martin-wagner/saba-6-3d-fernbedienung-hw/doku/latex/ant1.jpeg

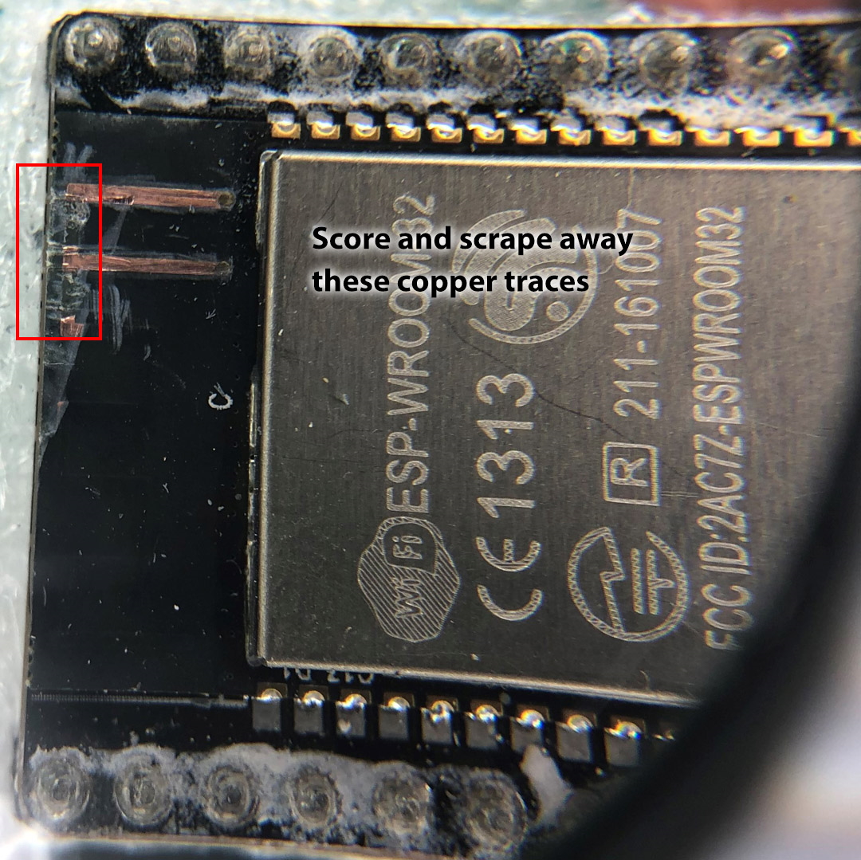
doku/latex/ant1.jpeg
