martin-wagner/saba-6-3d-fernbedienung-hw/doku/latex/ant2.jpeg

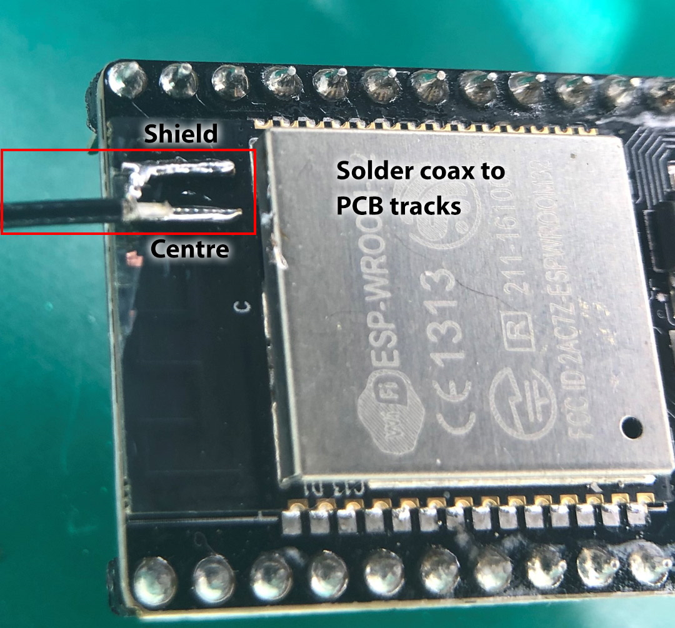
doku/latex/ant2.jpeg
