martin-wagner/saba-6-3d-fernbedienung-hw/doku/rechnungen-beispiele/2021-01-09 15.57.24 www.random-science-tools.com 3d192dff3986 suchlauf-langsam-schnell.jpg

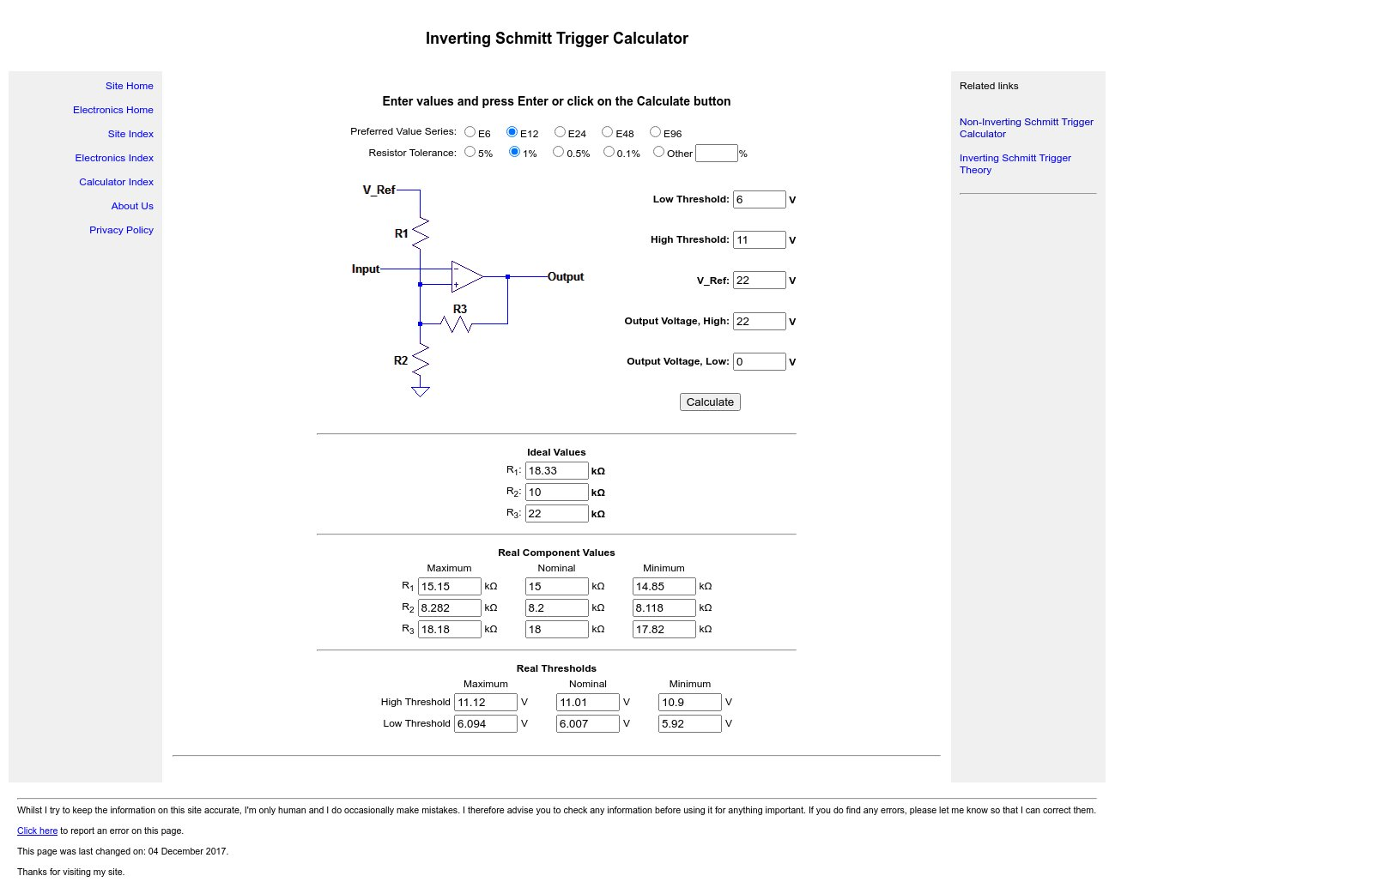
doku/rechnungen-beispiele/2021-01-09 15.57.24 www.random-science-tools.com 3d192dff3986 suchlauf-langsam-schnell.jpg
