martin-wagner/saba-6-3d-fernbedienung-hw/doku/rechnungen-beispiele/2021-04-10 11.28.31 www.random-science-tools.com 0c6ef2667732 phase-rev1b.jpg

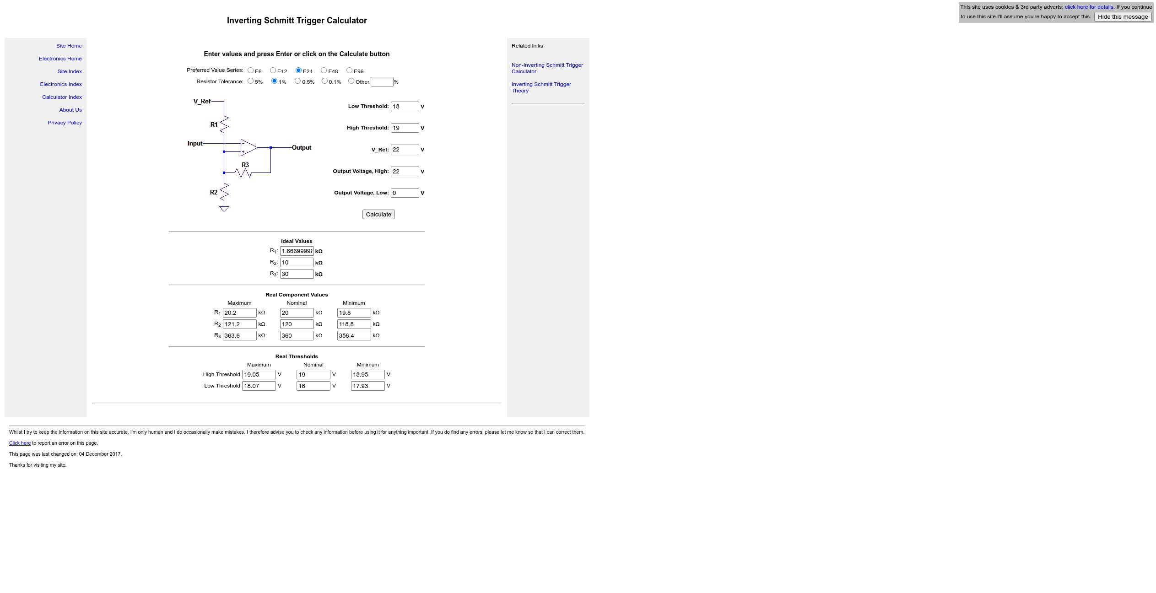
doku/rechnungen-beispiele/2021-04-10 11.28.31 www.random-science-tools.com 0c6ef2667732 phase-rev1b.jpg
