martin-wagner/saba-6-3d-fernbedienung-hw/doku/rechnungen-beispiele/2021-08-18 10.42.19 www.random-science-tools.com df0a42397f79 suchlauf-aus-langsam.jpg

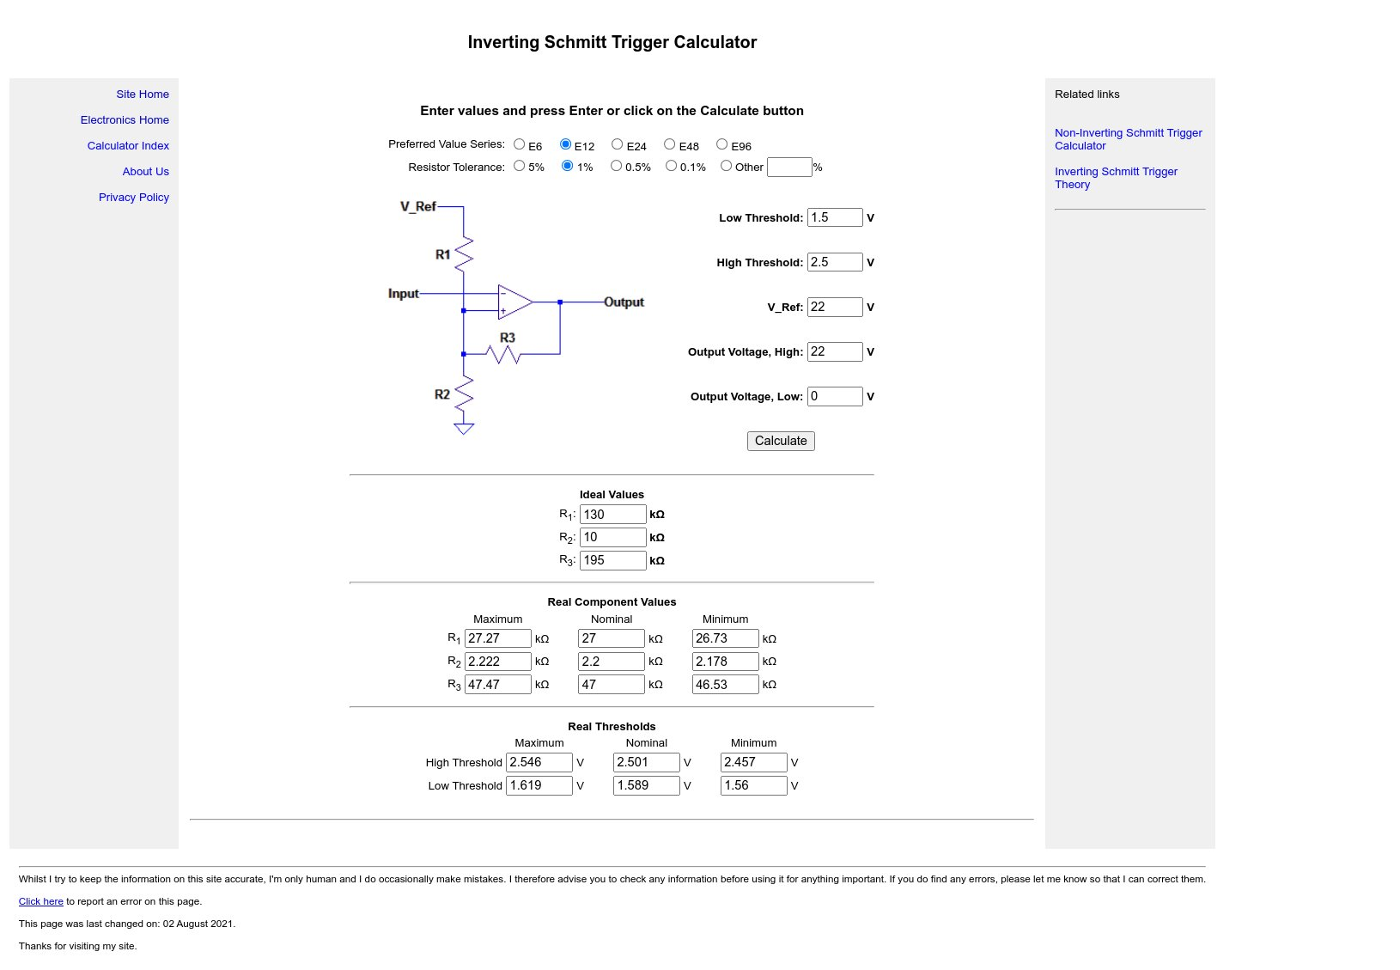
doku/rechnungen-beispiele/2021-08-18 10.42.19 www.random-science-tools.com df0a42397f79 suchlauf-aus-langsam.jpg
