martin-wagner/saba-6-3d-fernbedienung-hw/doku/rechnungen-beispiele/FB_Kontroller_Serie_5V.jpg

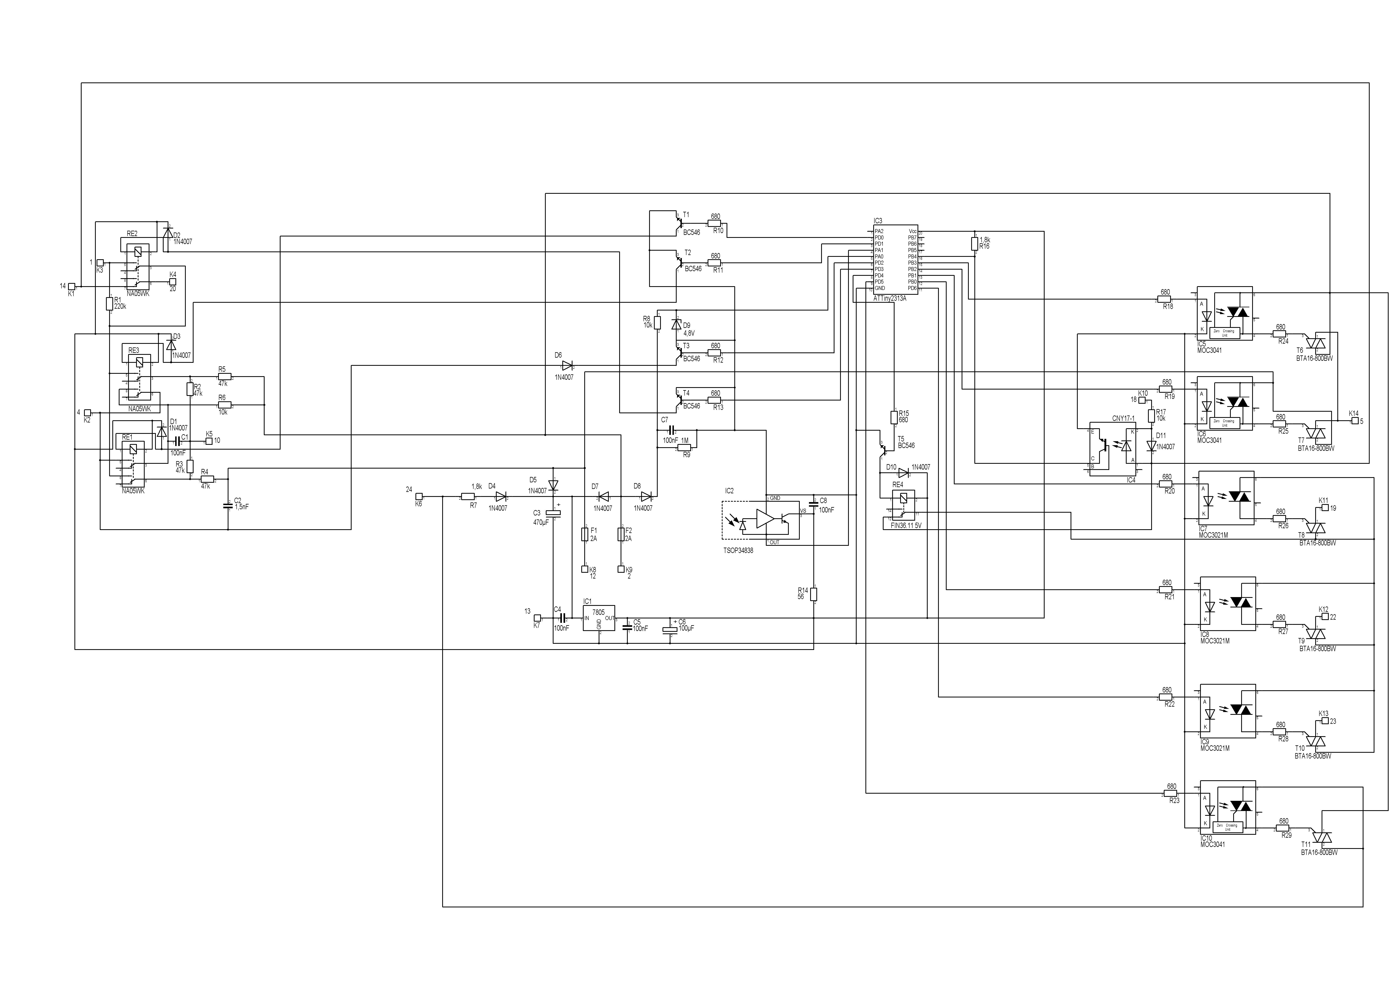
doku/rechnungen-beispiele/FB_Kontroller_Serie_5V.jpg
