martin-wagner/saba-6-3d-fernbedienung-hw/doku/rechnungen-beispiele/Saba_IR-Remote_Schema1.JPG

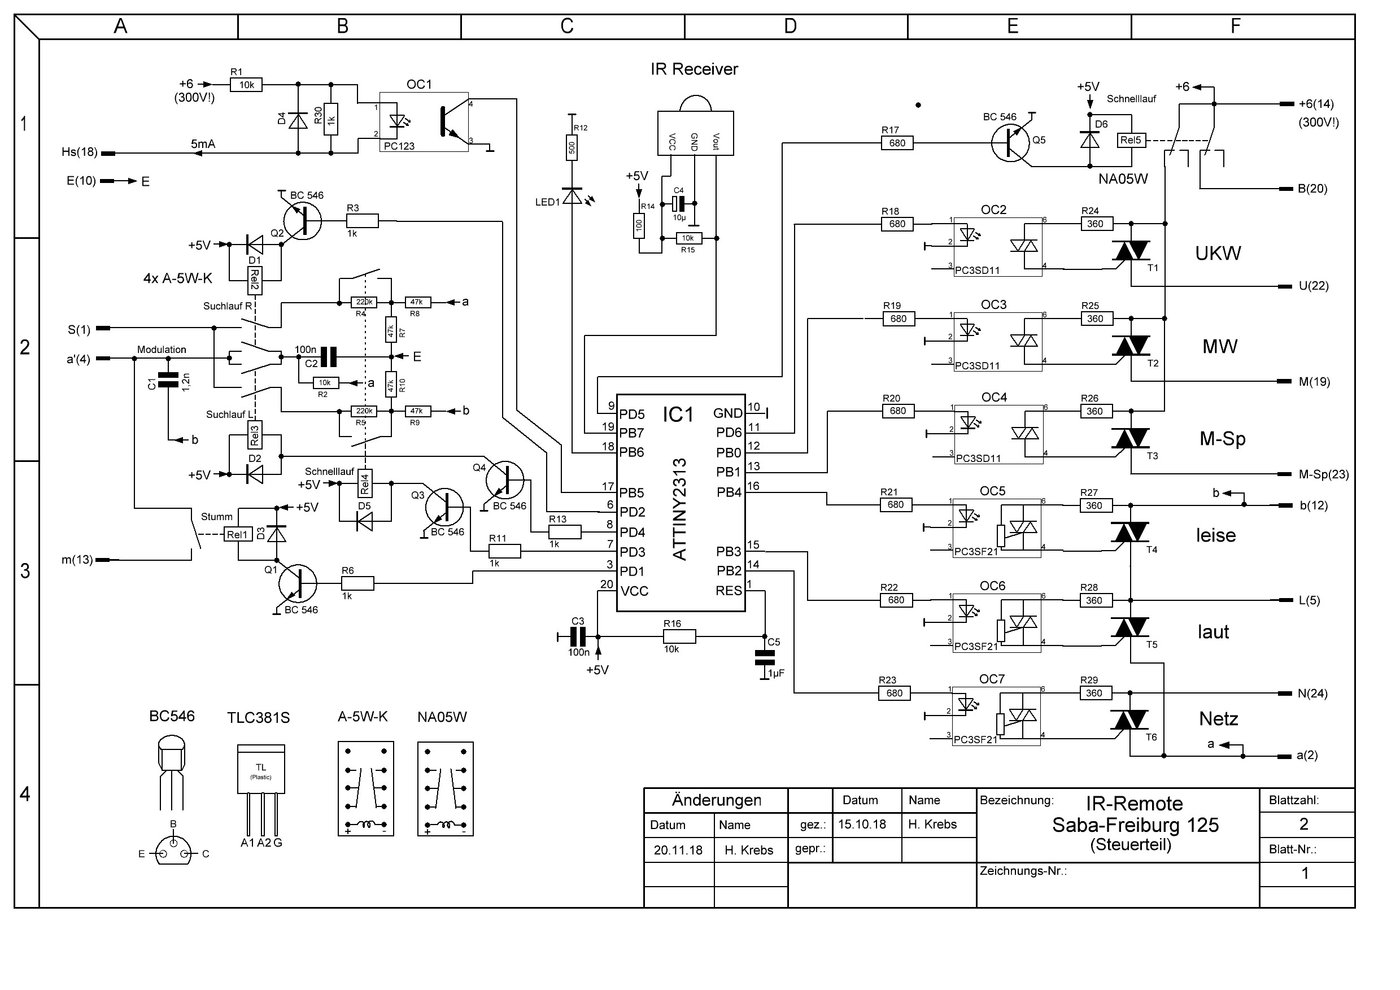
doku/rechnungen-beispiele/Saba_IR-Remote_Schema1.JPG
