martin-wagner/saba-6-3d-fernbedienung-hw/cad/pcb/saba-fernbedienung/rev1-a/scm/saba-fernbedienung.pdf

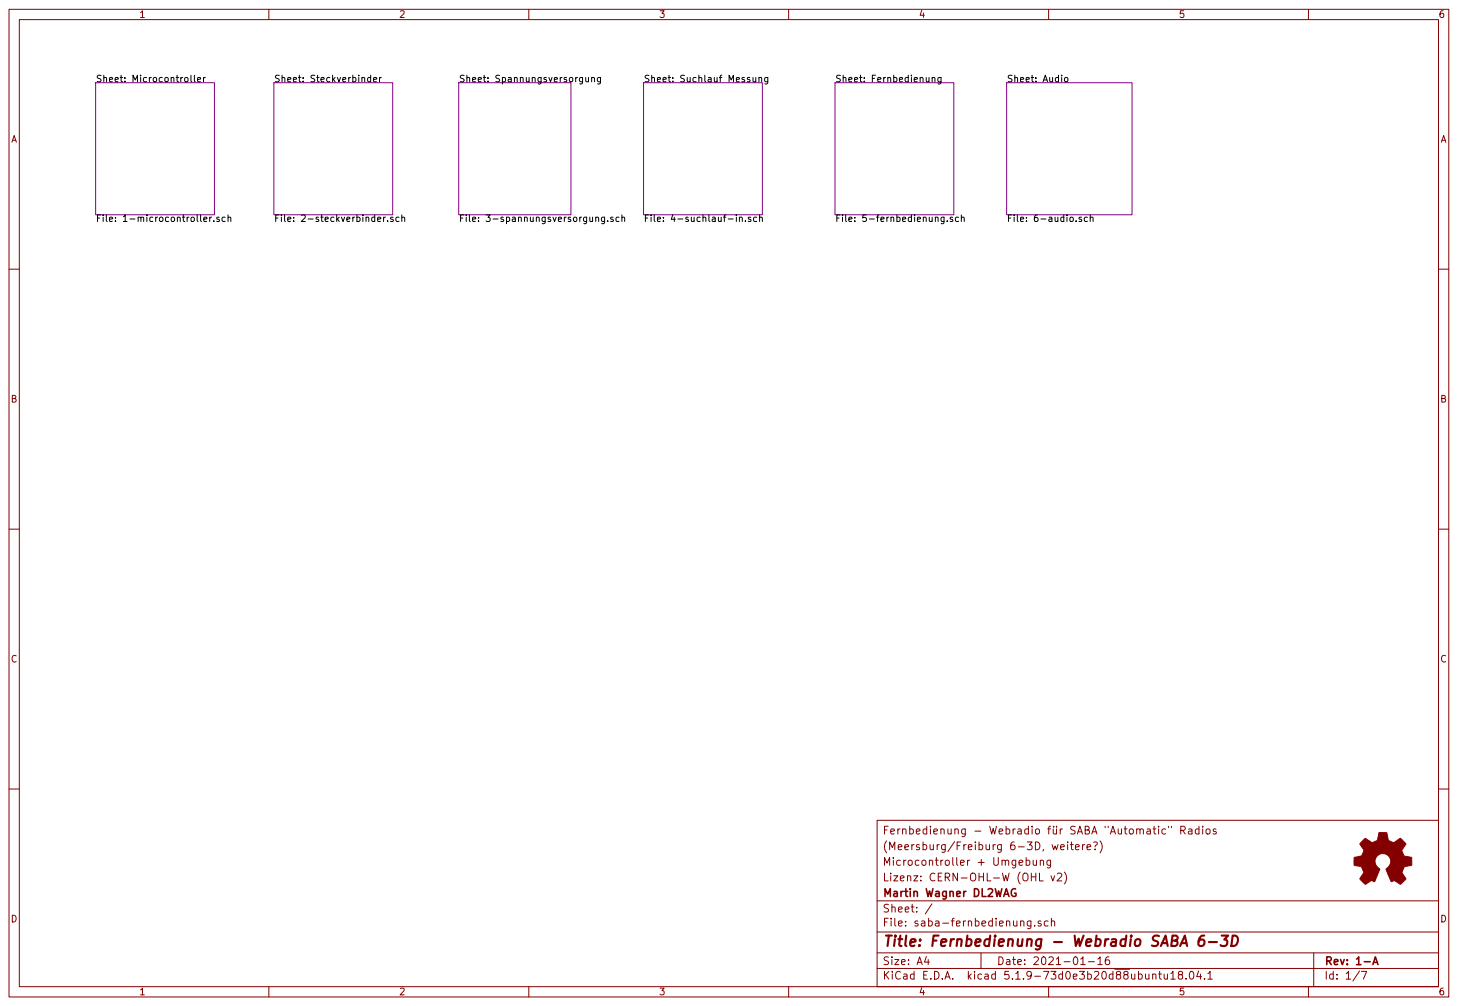
[picture p95: page 1]

Fernbedienung - Webradio für SABA "Automatic" Radios
(Meersburg/Freiburg 6-3D, weitere?)
Microcontroller + Umgebung
Lizenz: CERN-OHL-W (OHL v2)
File: saba-fernbedienung.sch Sheet: / Martin Wagner DL2WAG

Id: 1/7 Title: Fernbedienung - Webradio SABA 6-3D

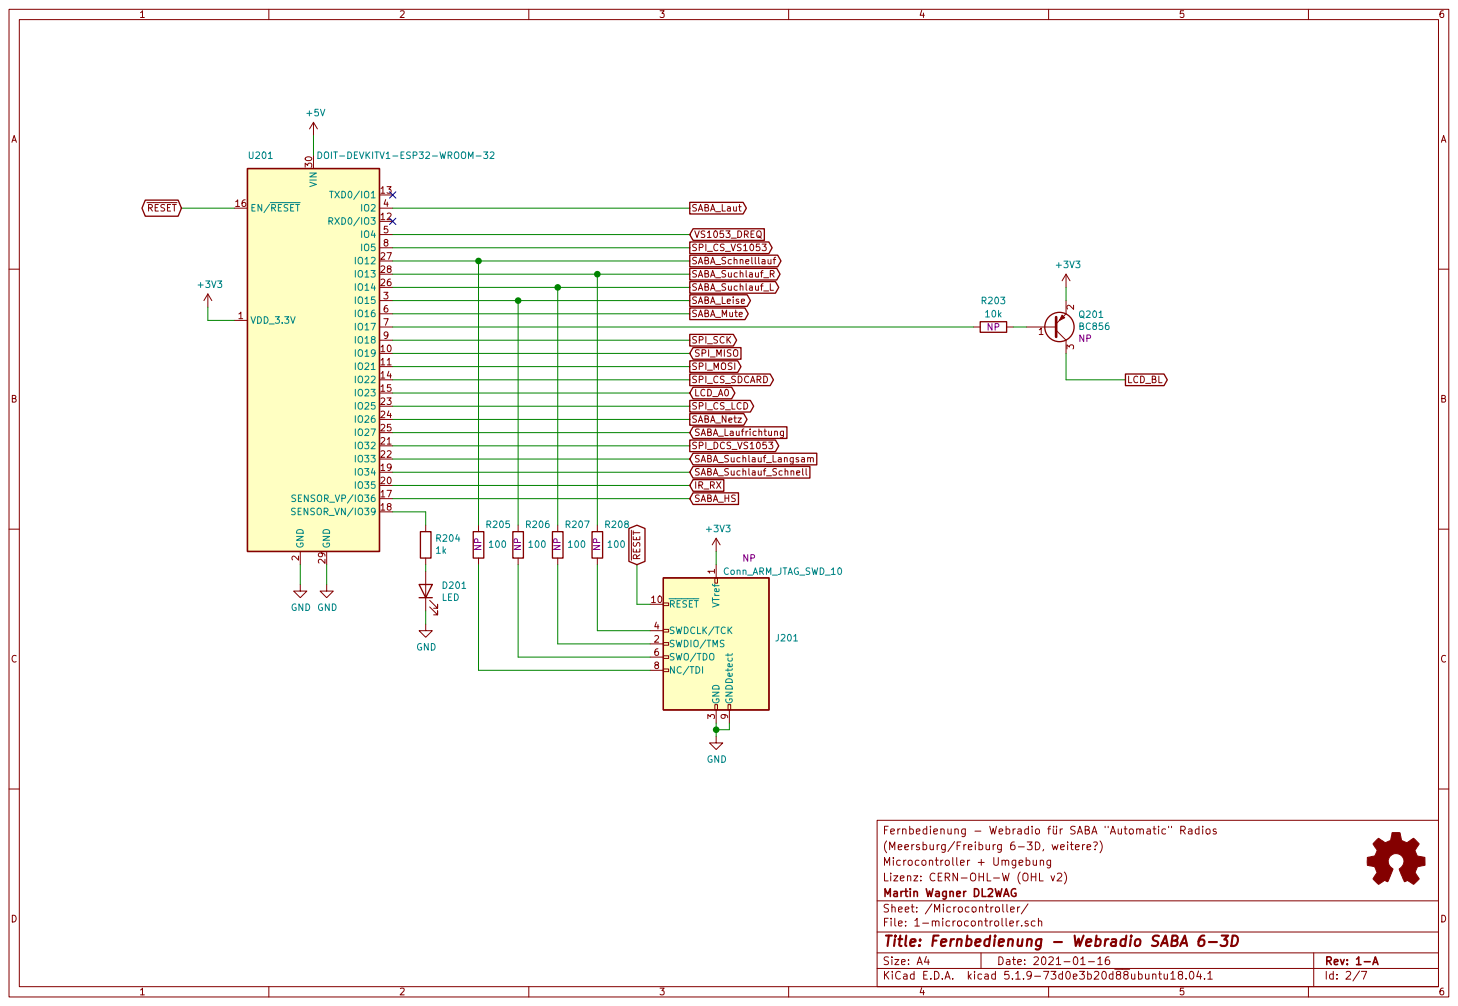
[picture p96: page 2]

3 SWDCLK/TCK 4 SWO/TDO 6 NC/TDI 8 GNDDetect 9

(Meersburg/Freiburg 6-3D, weitere?)
Microcontroller + Umgebung
Lizenz: CERN-OHL-W (OHL v2)
File: 1-microcontroller.sch Sheet: /Microcontroller/ Martin Wagner DL2WAG

Id: 2/7 Title: Fernbedienung - Webradio SABA 6-3D

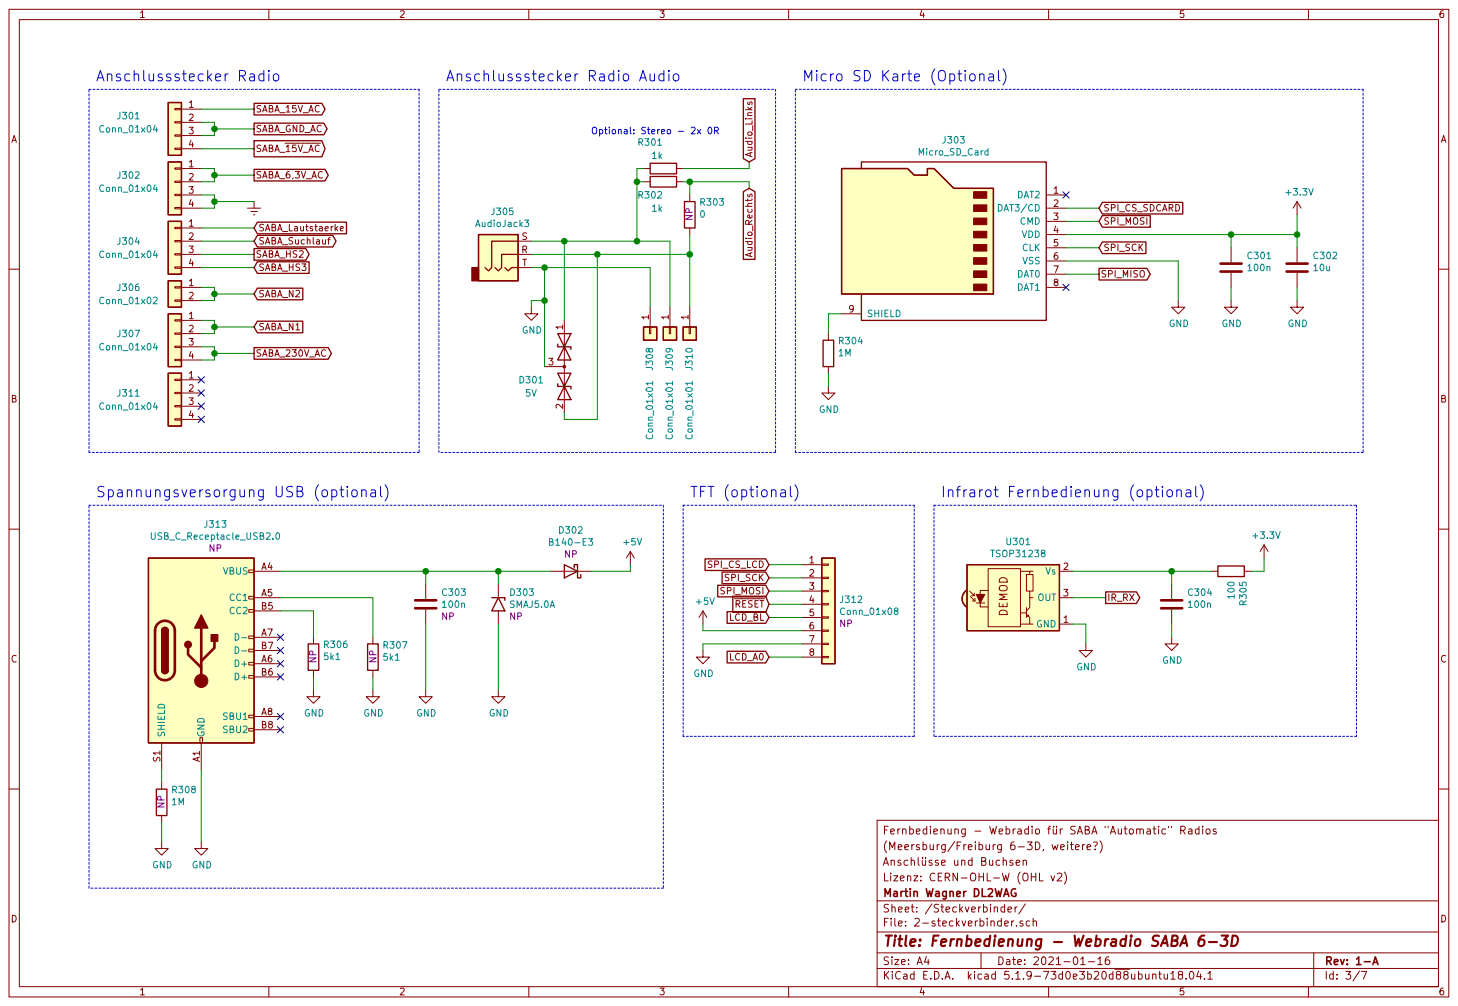
[picture p97: page 3]

Fernbedienung - Webradio für SABA "Automatic" Radios
(Meersburg/Freiburg 6-3D, weitere?)
Lizenz: CERN-OHL-W (OHL v2) Anschlüsse und Buchsen

File: 2-steckverbinder.sch Sheet: /Steckverbinder/ Martin Wagner DL2WAG

Id: 3/7 Title: Fernbedienung - Webradio SABA 6-3D

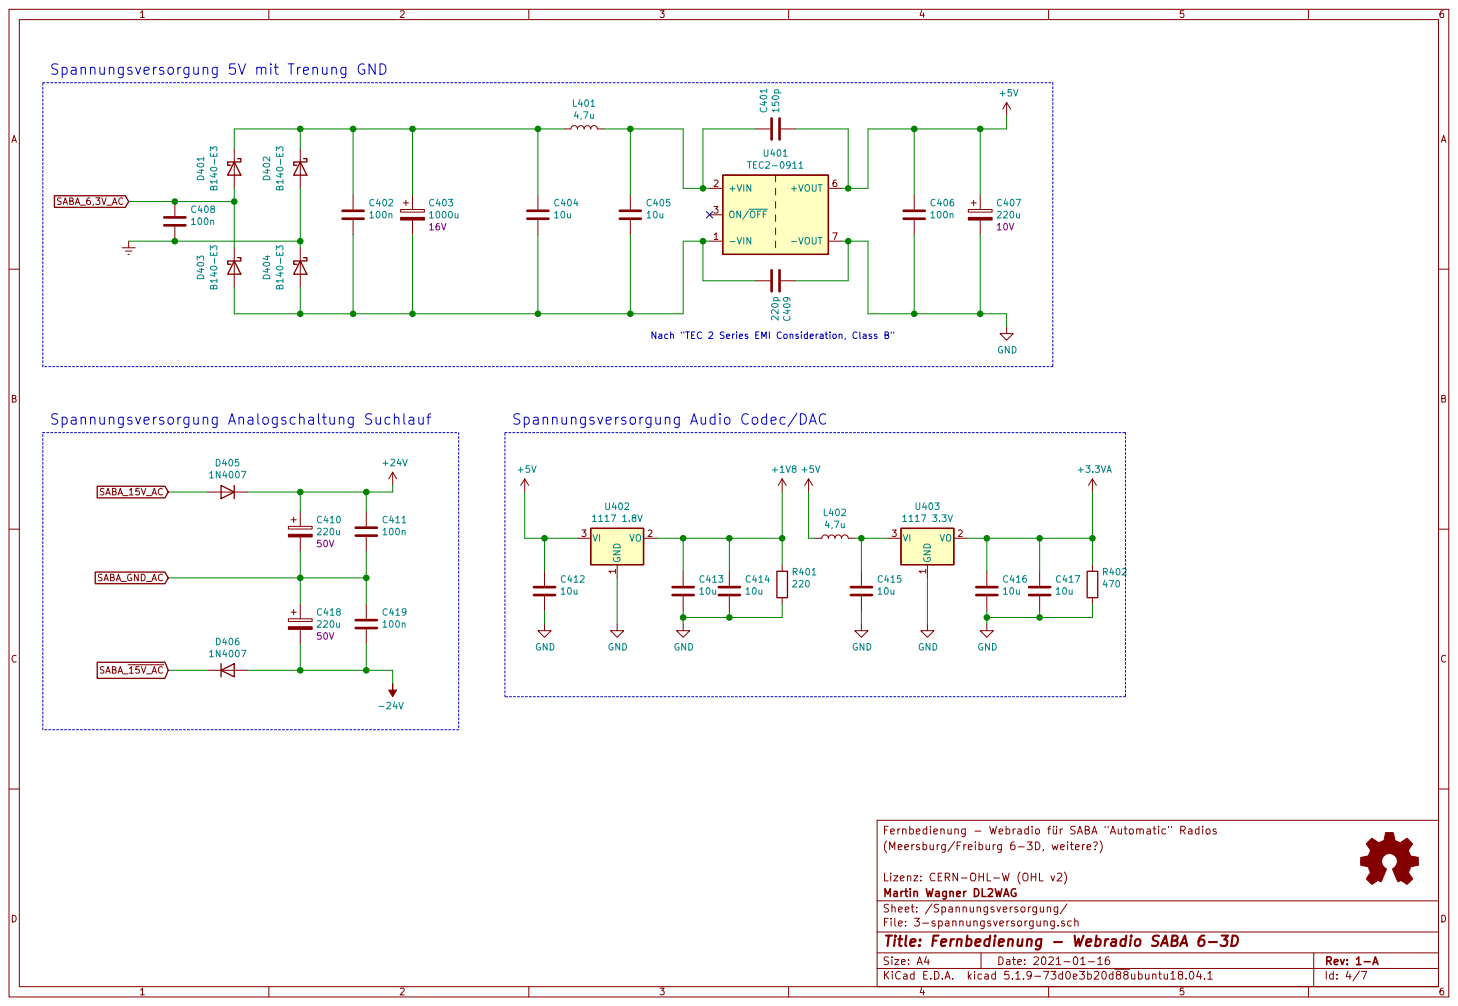
[picture p98: page 4]

Spannungsversorgung 5V mit Trenung GND

Nach "TEC 2 Series EMI Consideration, Class B" Spannungsversorgung Audio Codec/DAC

Fernbedienung - Webradio für SABA "Automatic" Radios
(Meersburg/Freiburg 6-3D, weitere?)

Lizenz: CERN-OHL-W (OHL v2)
Martin Wagner DL2WAG
Sheet: /Spannungsversorgung/
File: 3-spannungsversorgung.sch
Id: 4/7 Title: Fernbedienung - Webradio SABA 6-3D

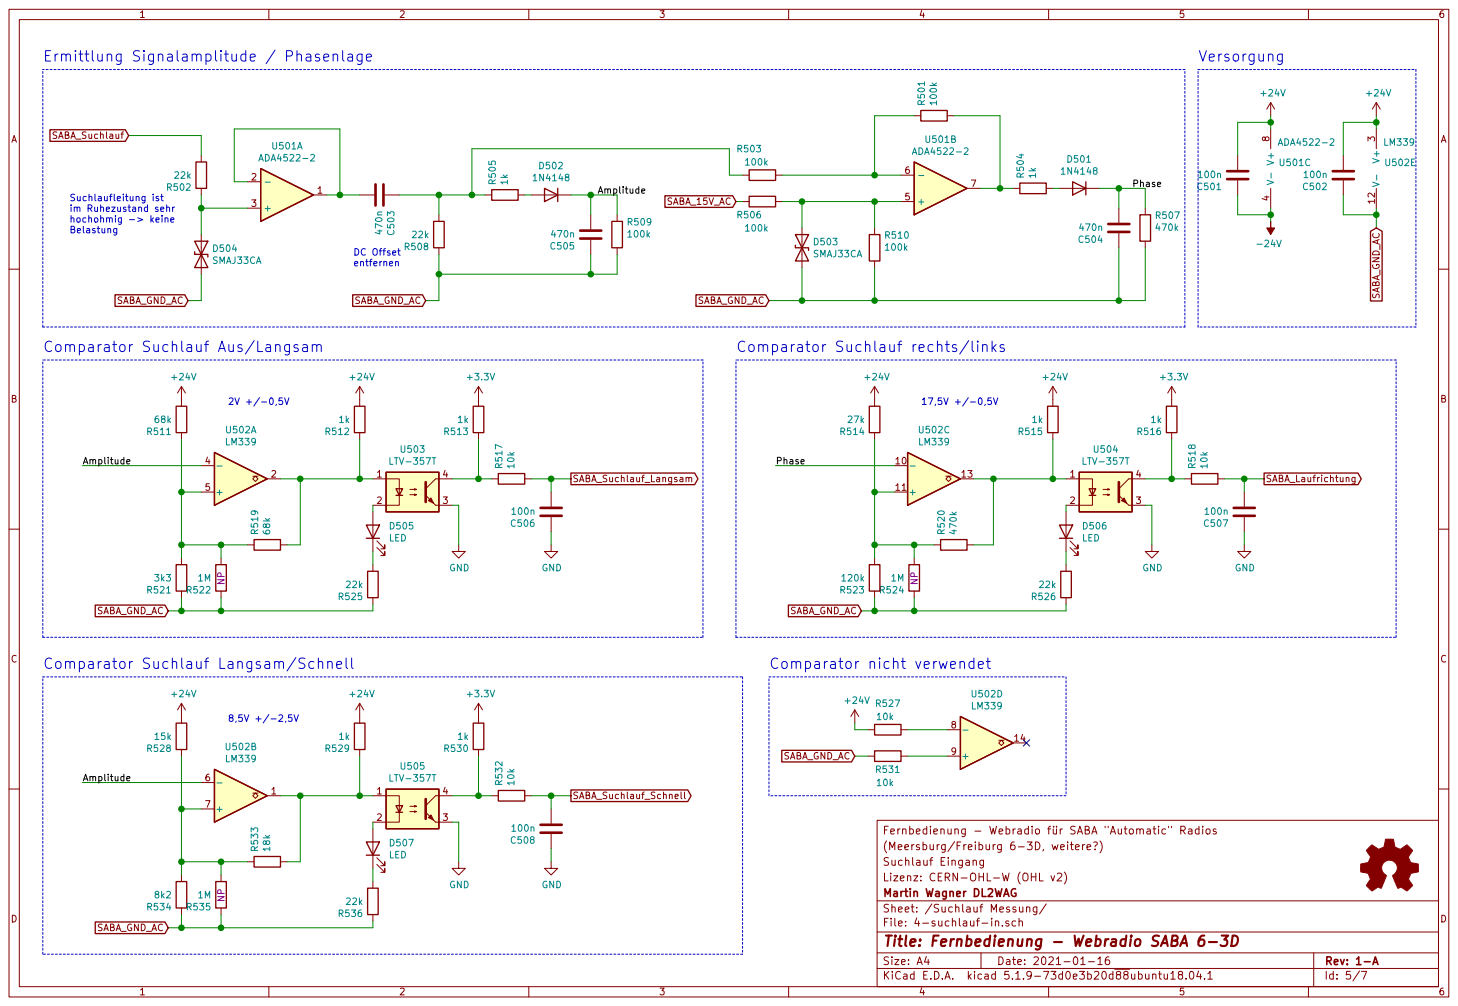
[picture p99: page 5]

Suchlaufleitung ist
im Ruhezustand sehr hochohmig -> keine

Comparator Suchlauf Aus/Langsam

Comparator Suchlauf rechts/links

2V +/-0,5V Comparator Suchlauf Langsam/Schnell

Fernbedienung - Webradio für SABA "Automatic" Radios R534

(Meersburg/Freiburg 6-3D, weitere?)
Suchlauf Eingang
Lizenz: CERN-OHL-W (OHL v2)
Martin Wagner DL2WAG
File: 4-suchlauf-in.sch Sheet: /Suchlauf Messung/
Id: 5/7 Title: Fernbedienung - Webradio SABA 6-3D

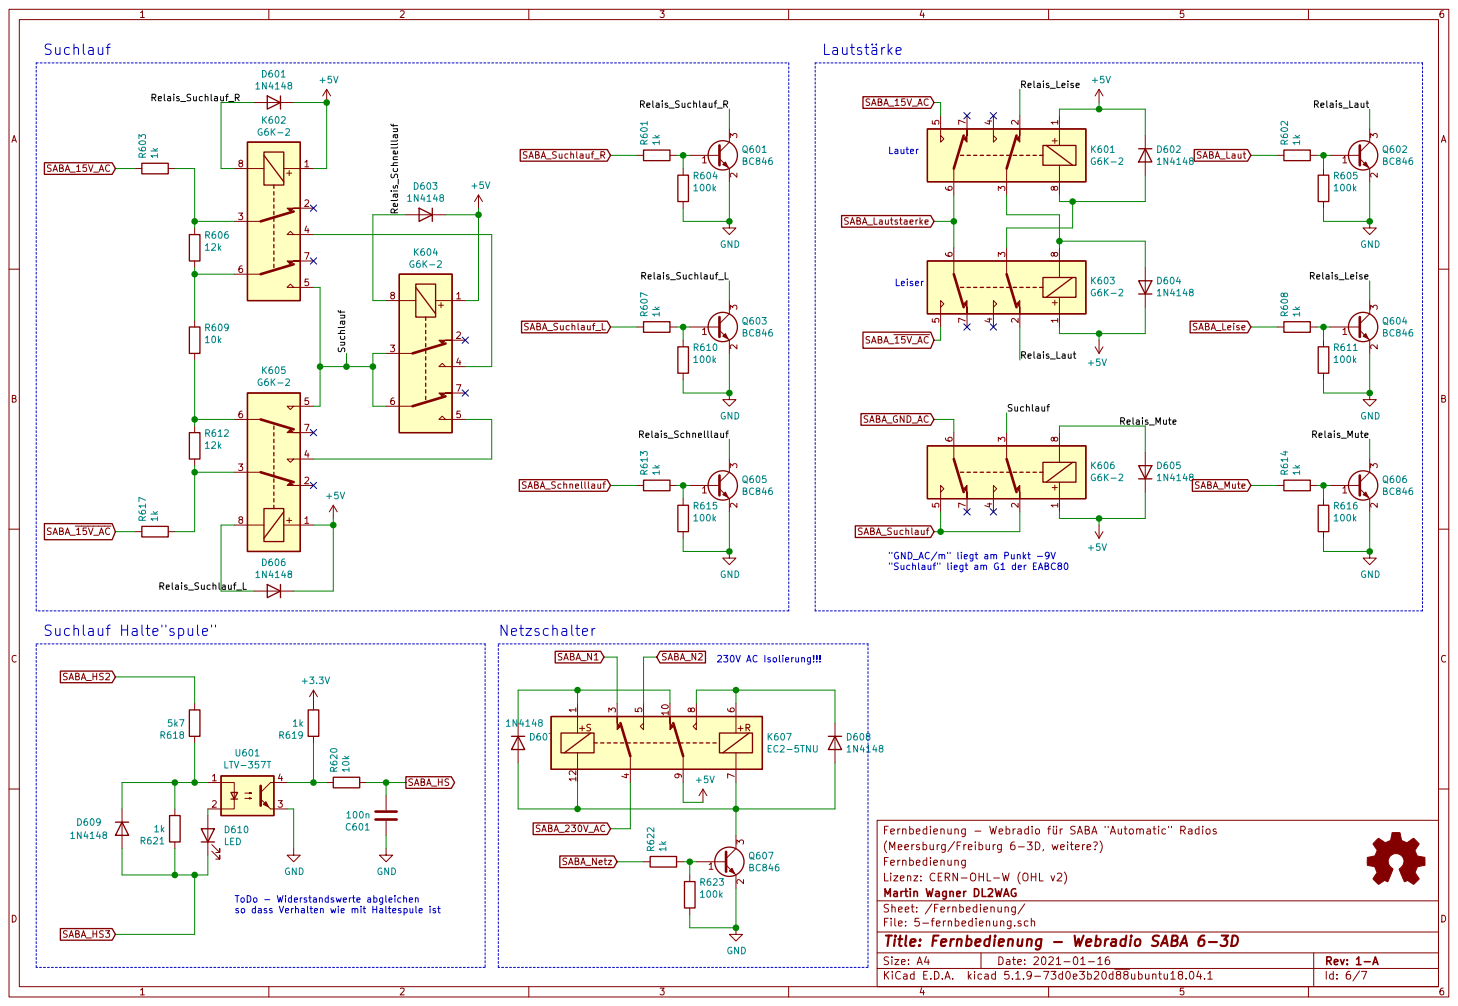
[picture p100: page 6]

Lauter Leiser "GND_AC/m" liegt am Punkt -9V

"Suchlauf" liegt am G1 der EABC80

Fernbedienung - Webradio für SABA "Automatic" Radios R619

(Meersburg/Freiburg 6-3D, weitere?)
Fernbedienung
Lizenz: CERN-OHL-W (OHL v2)
Martin Wagner DL2WAG
Sheet: /Fernbedienung/
File: 5-fernbedienung.sch
Id: 6/7 Title: Fernbedienung - Webradio SABA 6-3D

ToDo - Widerstandswerte abgleichen
so dass Verhalten wie mit Haltespule ist

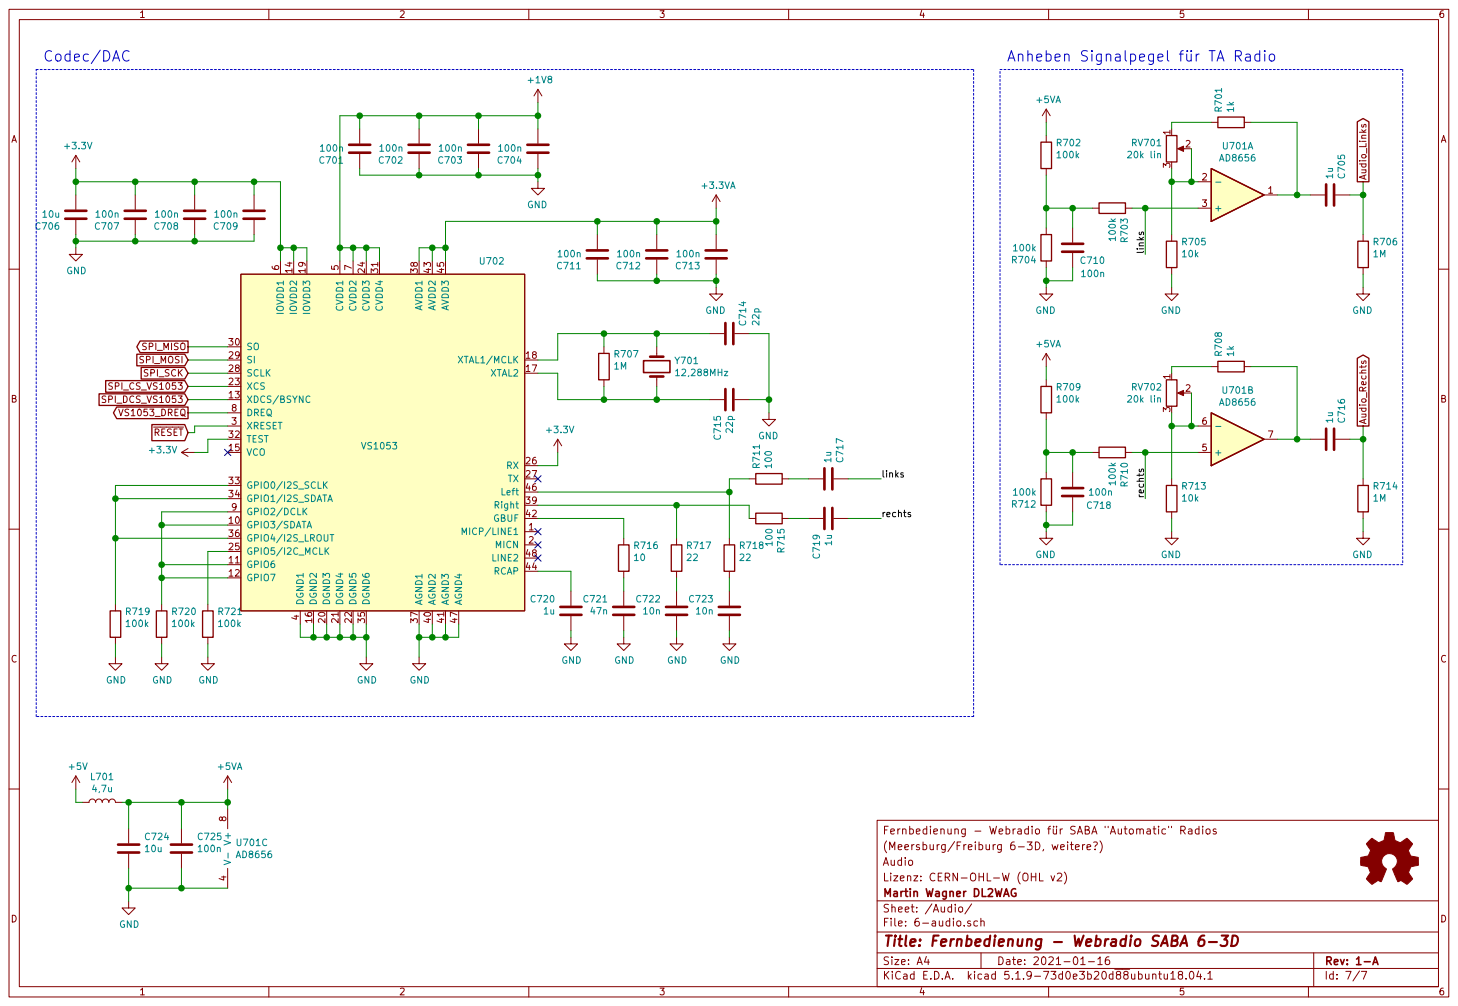
[picture p101: page 7]

7 DREQ 8 GPIO2/DCLK 9 U702 VS1053 GND GND GND GND

Fernbedienung - Webradio für SABA "Automatic" Radios
(Meersburg/Freiburg 6-3D, weitere?)
Lizenz: CERN-OHL-W (OHL v2) Audio

File: 6-audio.sch Sheet: /Audio/ Martin Wagner DL2WAG

Id: 7/7 Title: Fernbedienung - Webradio SABA 6-3D
