martin-wagner/saba-6-3d-fernbedienung-hw/simulation/suchlauf_schalter_digital.asc

C1: cap; 50µ
C2: cap; 50µ
C3: cap; 100µ
C4: cap; 470n
C5: cap; 100µ
C6: cap; 100n
C7: cap; 250n
C8: cap; 100n
C9: cap; 470n
C10: cap; 470n
D1: diode
D2: schottky; MBRS1100
D3: zener; TFZ39B
D4: zener; TFZ39B
D5: schottky; MBRS1100
D6: diode; 1N4148
D7: diode; 1N4148
D8: zener; TFZ39B
D9: zener; TFZ39B
R1: res; 1k
R2: res; 1k
R3: res; 12k5
R4: res; 10k
R5: res; 12k5
R6: res; 2k
R7: res; 25k
R8: res; 30k
R9: res; 5Meg
R10: res; 1Meg
R11: res; 2Meg
R12: res; 100k
R13: res; 1m
R14: res; 22k
R15: res; 1k
R16: res; 2Meg
R17: res; 2Meg
R18: res; 22k
R19: res; 100k
R20: res; 100k
R21: res; 100k
R22: res; 100k
R23: res; 1Meg
R24: res; 1k
S1: sw; MYSW
S2: sw; MYSW
S3: sw; MYSW
S4: sw; MYSW
U1: ADA4522
U2: ADA4522
V1: voltage; SINE(0 21 50 0 0 0 1000)
V2: voltage; SINE(0 21 50 0 0 0 1000)
V3: voltage; PULSE(0 1 1 1m 1m 1 10 1)
V4: voltage; PULSE(0 1 1 1m 1m 1 2 2)
V5: voltage; PULSE(0 1 7 1m 1m 1 2 2)
V6: voltage; PULSE(0 1 7 1m 1m 1 10 1)
Named nets: m, a, b, s, +vs, out_aplitude, 0, G1, saba_gnd, -vs, out_pase, s1, s2, s3, s4
.tran 10
links suchen S2
links laufen S1 + S2
rechts suchen S3
rechts laufen S3 + S4
Buffer
s1
s2
s3
s4
.model MYSW SW(Ron=1m Roff=100Meg Vt=.5 Vh=-.4)
