martin-wagner/saba-6-3d-fernbedienung-hw/simulation/suchlauf_schalter.asc

C1: cap; 50µ
C2: cap; 50µ
C3: cap; 250n
D1: diode
R1: res; 1k
R2: res; 1k
R3: res; 12k5
R4: res; 10k
R5: res; 12k5
R6: res; 2k
R7: res; 25k
R8: res; 30k
R9: res; 5Meg
R10: res; 1Meg
R11: res; 2Meg
R12: res; 2Meg
R13: res; 2Meg
V1: voltage; SINE(0 21 50 0 0 0 1000)
V2: voltage; SINE(0 21 50 0 0 0 1000)
Named nets: 0, m, a, b, s, s1, s2, s3, s4, G1, saba_gnd
.tran 5
links suchen S2
links laufen S1 + S2
rechts suchen S3
rechts laufen S3 + S4
